madnerdorg/openlight/Arduino/openlight_gateway/secrets.h

// Put your own code here
// You don't need to put the last number as it will be increment each times you send a code
int on [7] = { 0x00,0x00,0x00,0x00,0x00,0x00,0x00 };
int off [7] = { 0x00,0x00,0x00,0x00,0x00,0x00,0x00 };
